corygrant/dingoPDM-Max/dingoPDM-Max/Models/7461084_Download_STP_7461084_rev1.stp

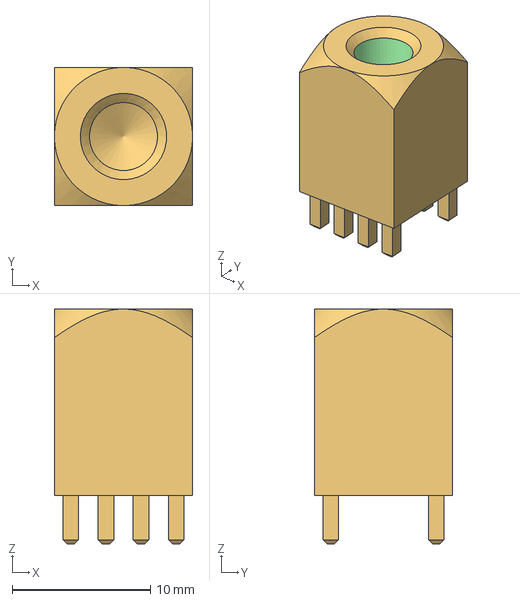
[picture p19: CAD file, 2024-07-14]
dingoPDM-Max/Models/7461084_Download_STP_7461084_rev1.stp
10.0 x 10.0 x 17.0 mm
